rexxar-tc/IoDriver/Hardware/PCB-Bottom.bmp

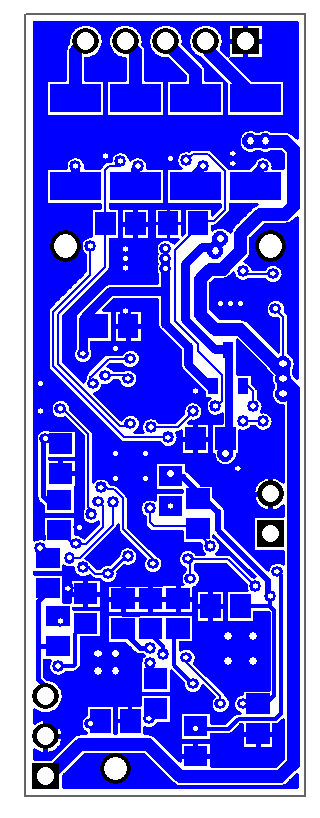
Hardware/PCB-Bottom.bmp
